naomisilver/Novostok/assets/images/Enclosure - shoulder ground and kapton tape.jpg

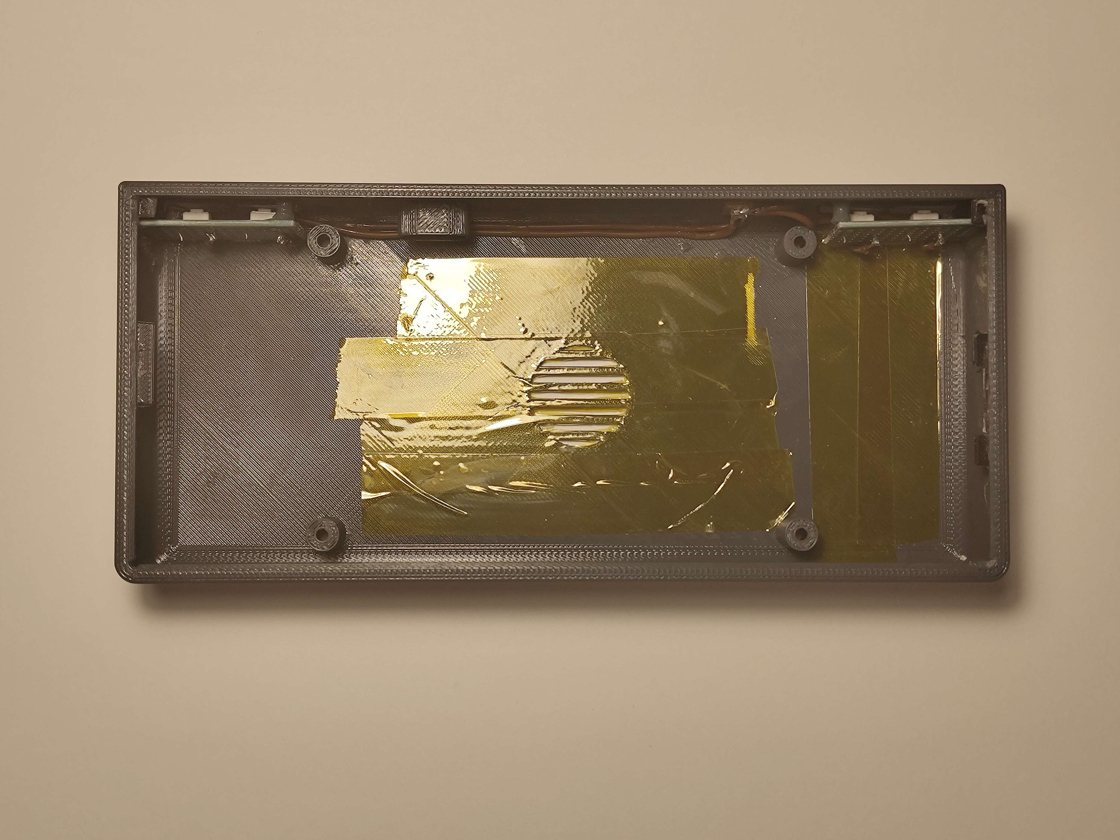
assets/images/Enclosure - shoulder ground and kapton tape.jpg
