naomisilver/Novostok/assets/images/Faceplate - pcbs.jpg

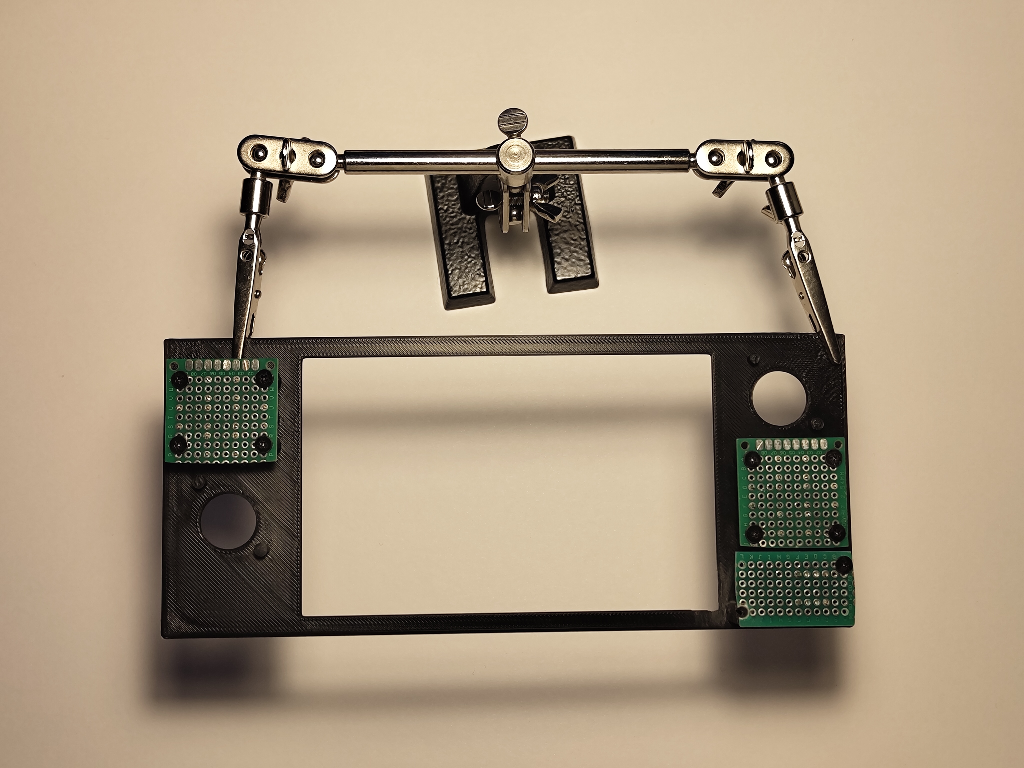
assets/images/Faceplate - pcbs.jpg
