naomisilver/Novostok/assets/images/The Novostok.jpg

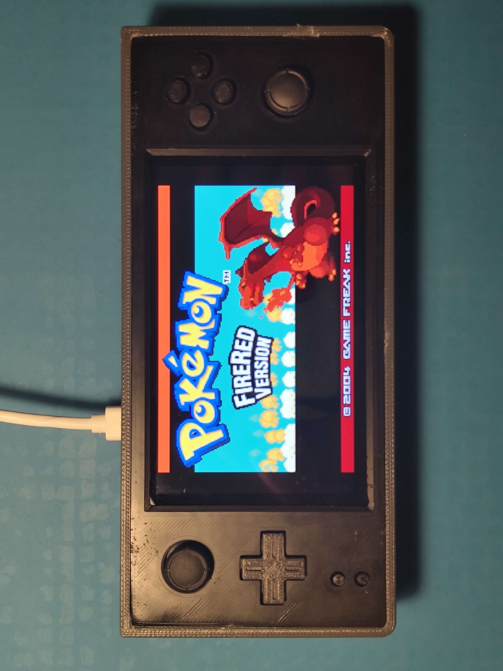
assets/images/The Novostok.jpg
