naomisilver/Novostok/assets/images/Enclosure - Pico mounted shoulders soldered.jpg

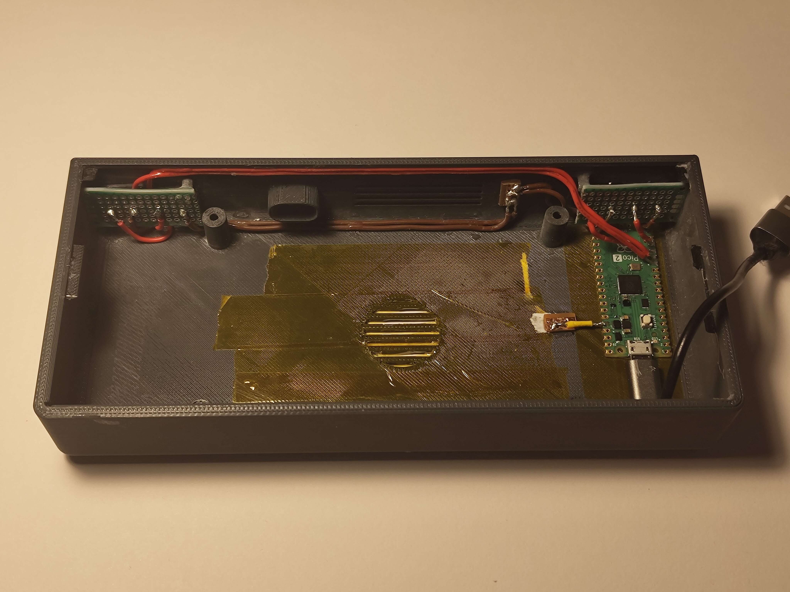
assets/images/Enclosure - Pico mounted shoulders soldered.jpg
