naomisilver/Novostok/assets/images/Faceplate - Analogue wiring.jpg

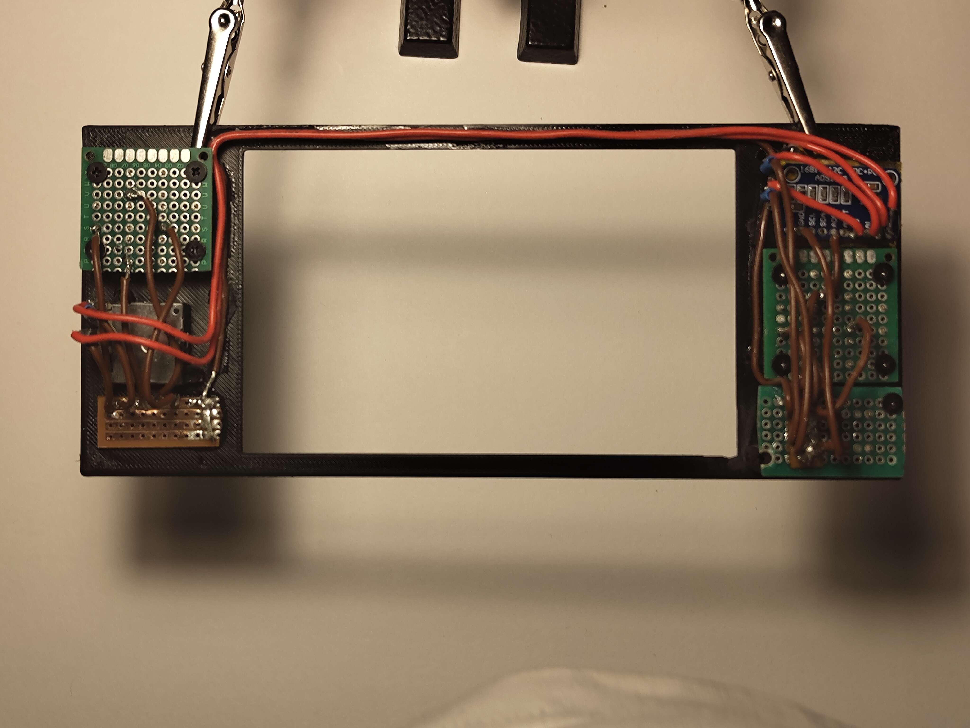
assets/images/Faceplate - Analogue wiring.jpg
