naomisilver/Novostok/assets/images/Faceplate and enclosure - ADS soldered.jpg

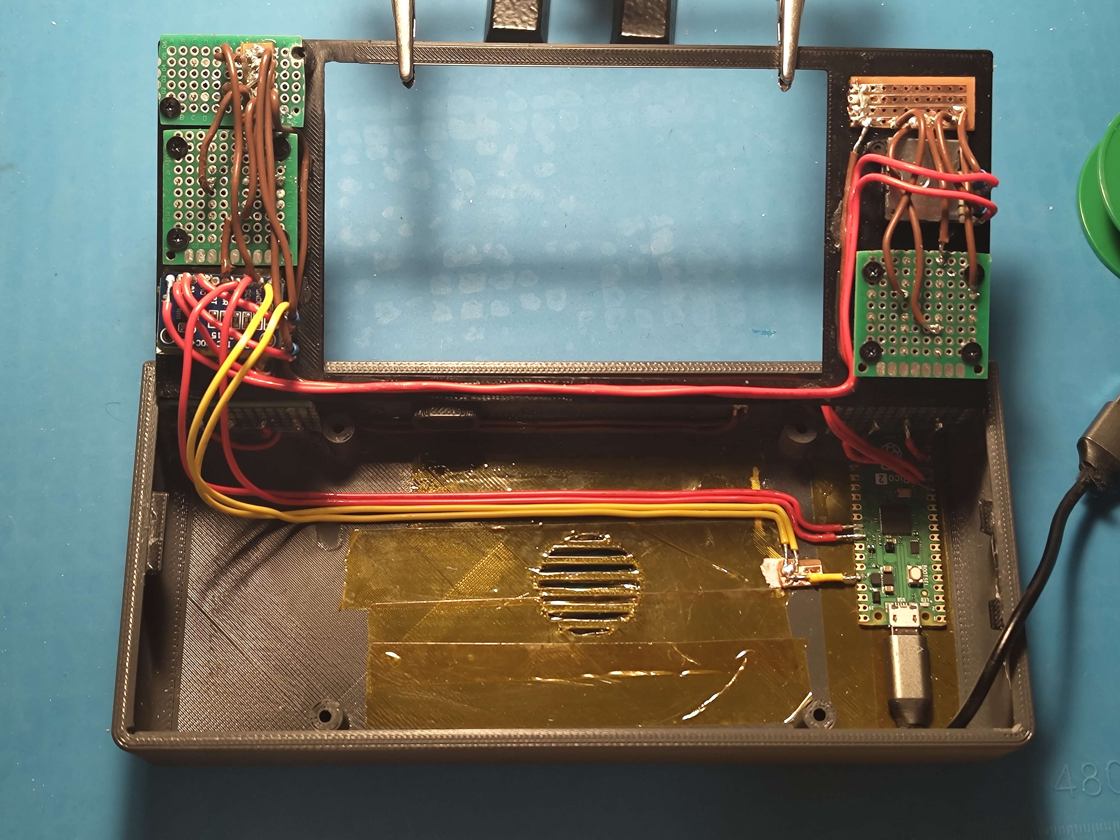
assets/images/Faceplate and enclosure - ADS soldered.jpg
