naomisilver/Novostok/assets/images/Faceplate and enclosure - left side soldered.jpg

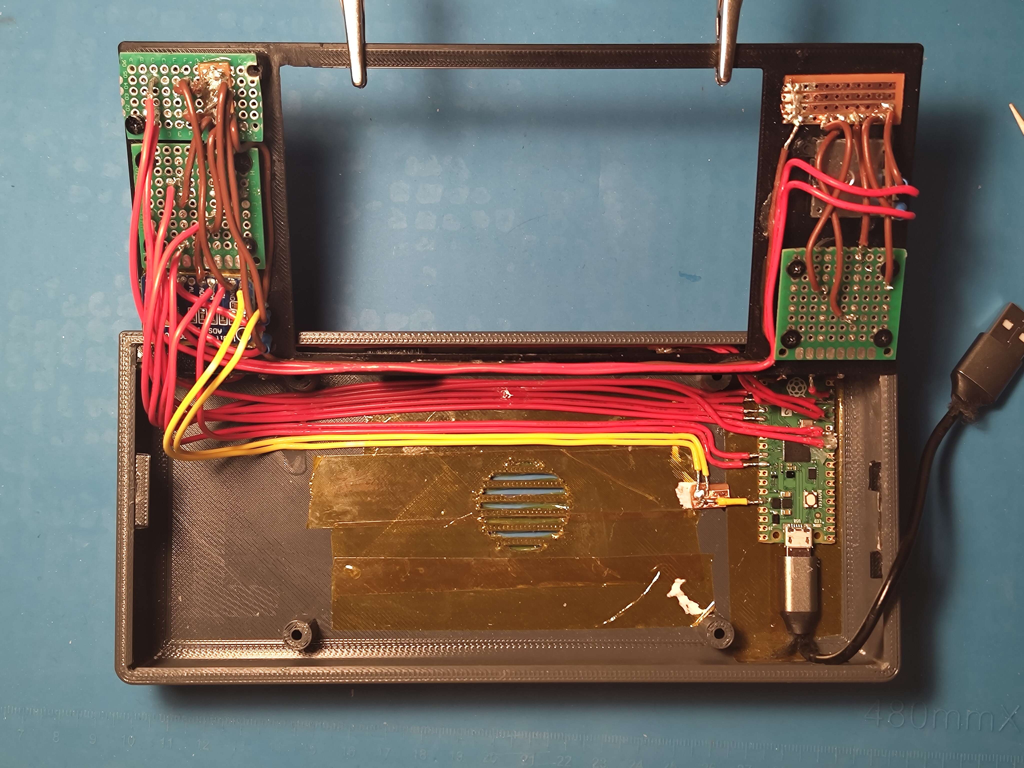
assets/images/Faceplate and enclosure - left side soldered.jpg
