naomisilver/Novostok/assets/images/PCB Guide.png

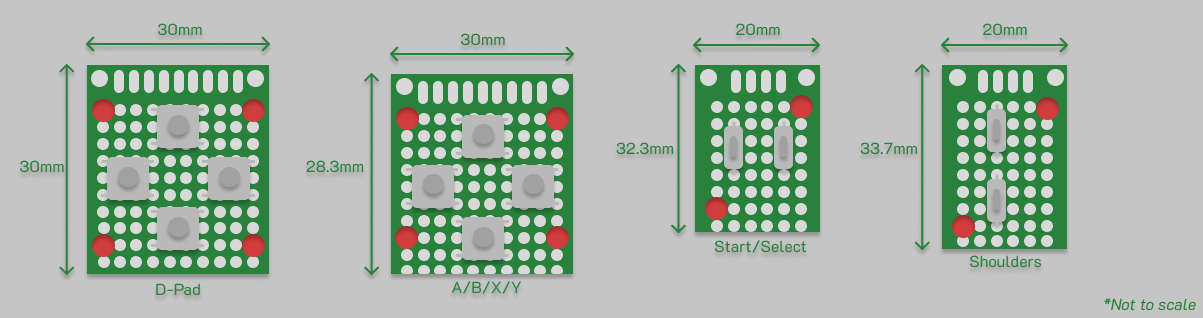
assets/images/PCB Guide.png
