naomisilver/Novostok/assets/images/Novostok - input testing.jpg

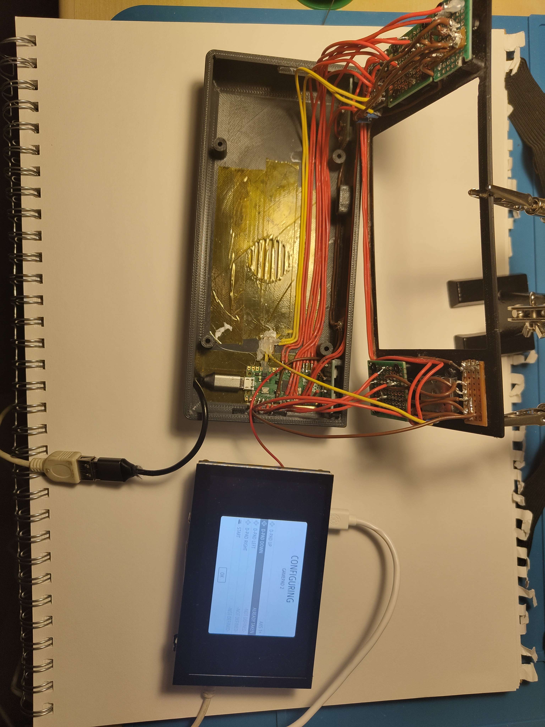
assets/images/Novostok - input testing.jpg
